mike-ady/Stenokey/Key_Print_Files/FingerWideLeft.stl

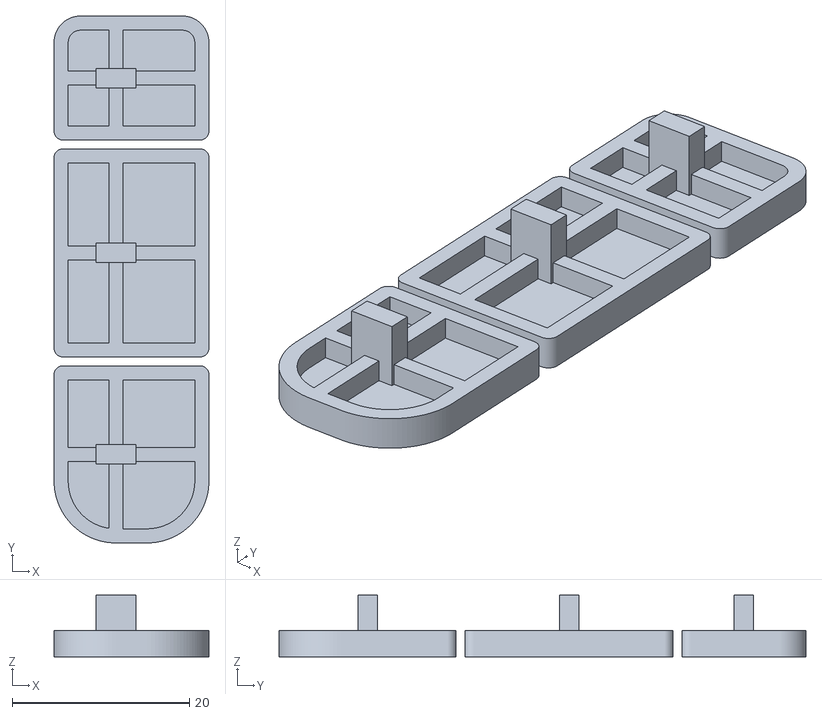
[picture p19: CAD file, 2017-11-08]
Key_Print_Files/FingerWideLeft.stl
17.5 x 59.5 x 7.00
