mike-ady/Stenokey/PCB.stl

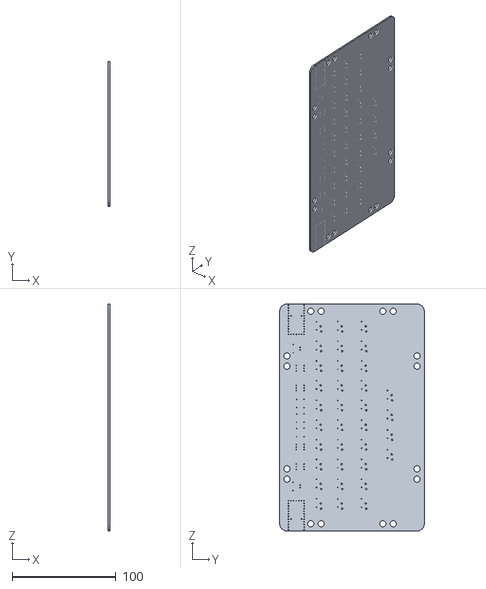
[picture p20: CAD file, 2017-11-08]
PCB.stl
1.60 x 139.5 x 219.0
