mike-ady/Stenokey/Key_Print_Files/KeyUpperWideLeftExtended.stl

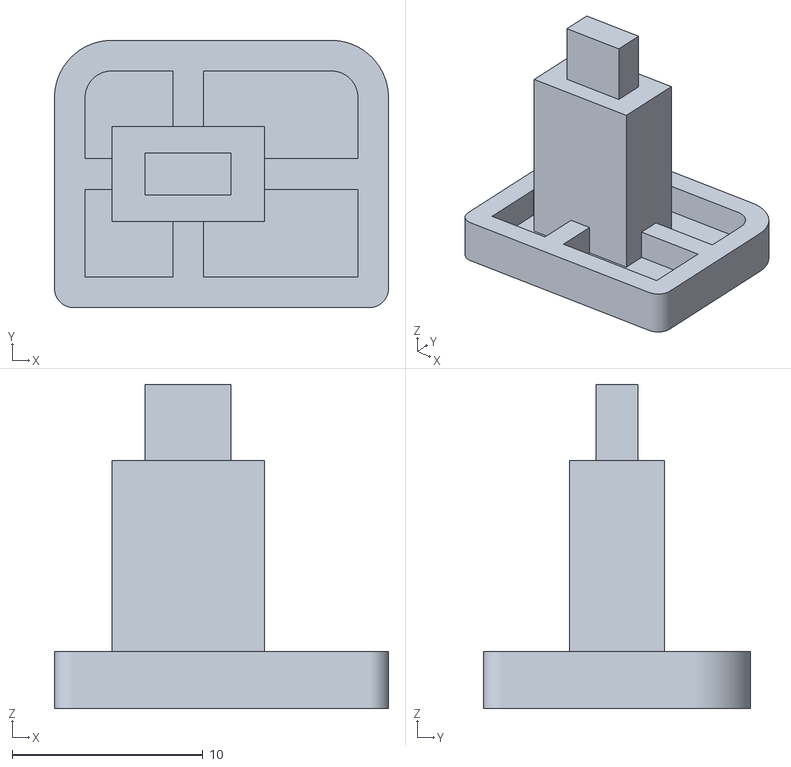
[picture p21: CAD file, 2017-11-08]
Key_Print_Files/KeyUpperWideLeftExtended.stl
17.5 x 14.0 x 17.0
