mike-ady/Stenokey/Key_Print_Files/KeyLowerWideLeftExtended.stl

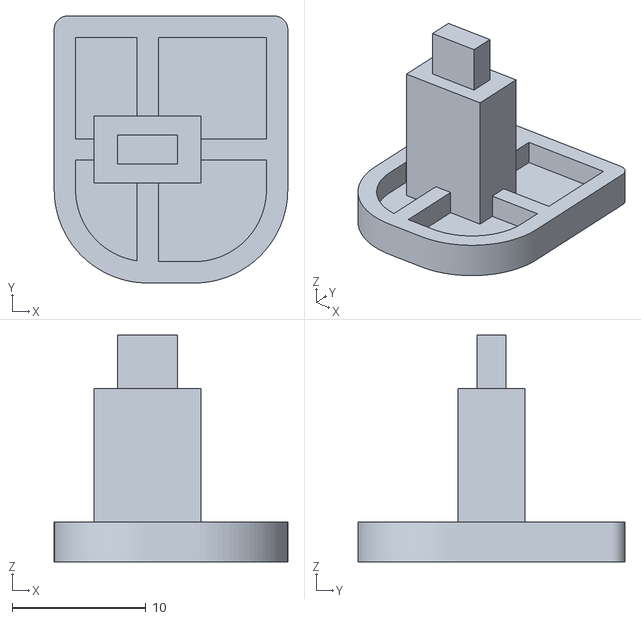
[picture p22: CAD file, 2017-11-08]
Key_Print_Files/KeyLowerWideLeftExtended.stl
17.5 x 20.0 x 17.0
