mike-ady/Stenokey/Key_Print_Files/KeyMiddleWideRightExtended.stl

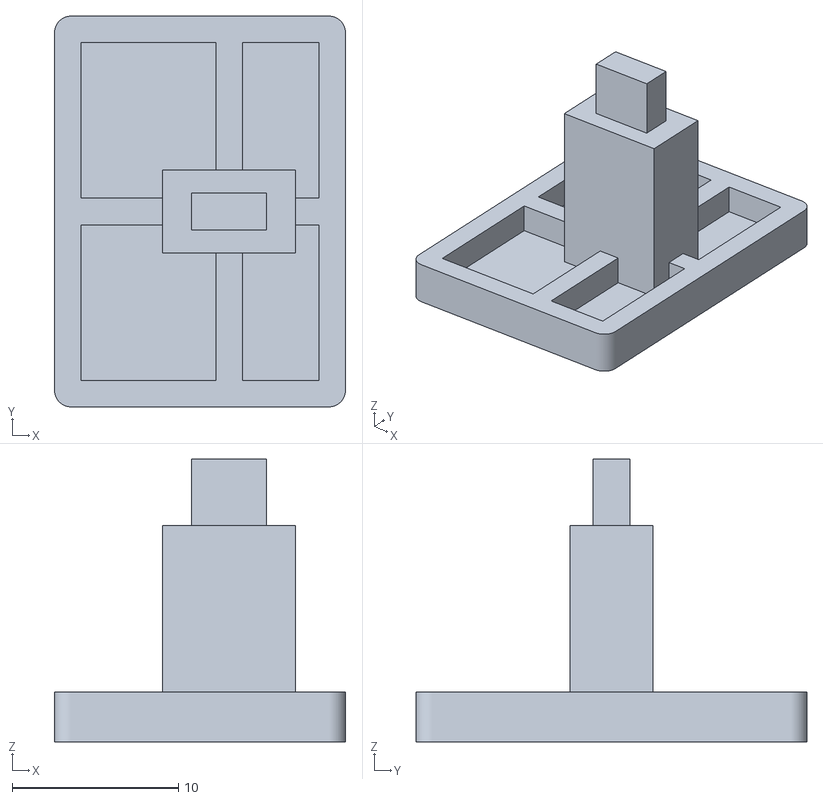
[picture p23: CAD file, 2017-11-08]
Key_Print_Files/KeyMiddleWideRightExtended.stl
17.5 x 23.5 x 17.0
