mike-ady/Stenokey/Key_Print_Files/FingerNarrow.stl

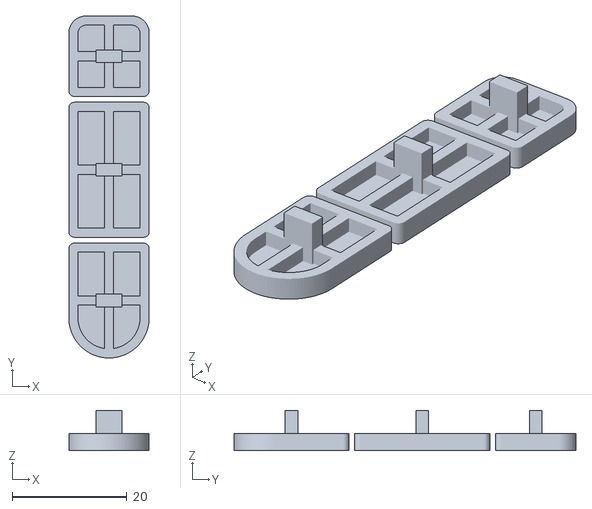
[picture p24: CAD file, 2017-11-08]
Key_Print_Files/FingerNarrow.stl
14.0 x 59.5 x 7.00
