mike-ady/Stenokey/Key_Print_Files/KeyLowerDouble.stl

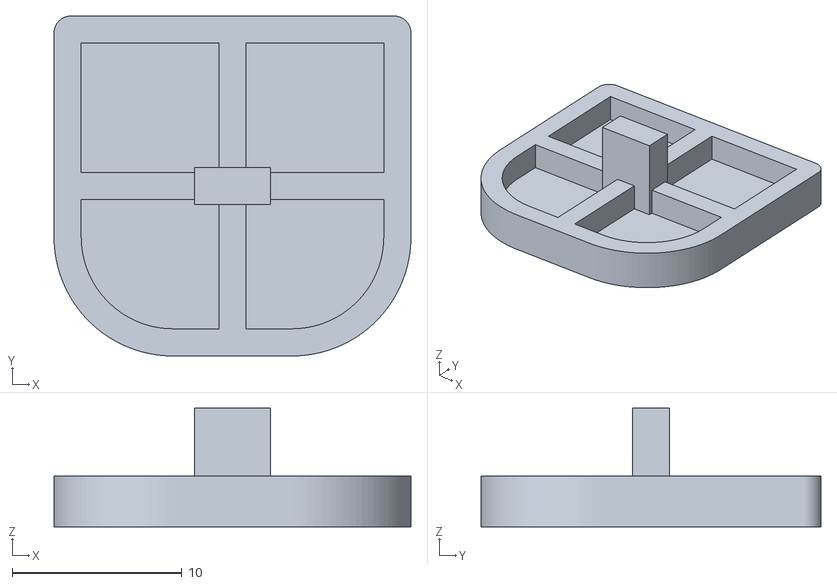
[picture p25: CAD file, 2017-11-08]
Key_Print_Files/KeyLowerDouble.stl
21.0 x 20.0 x 7.00
