mike-ady/Stenokey/Key_Print_Files/FingerDouble.stl

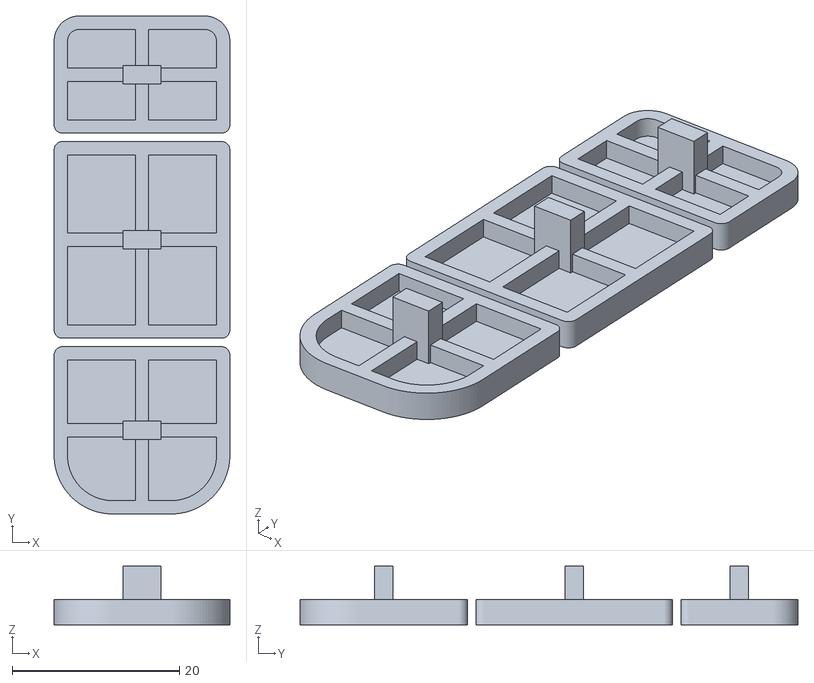
[picture p26: CAD file, 2017-11-08]
Key_Print_Files/FingerDouble.stl
21.0 x 59.5 x 7.00
