mike-ady/Stenokey/Key_Print_Files/KeyUpperNarrowExtended.stl

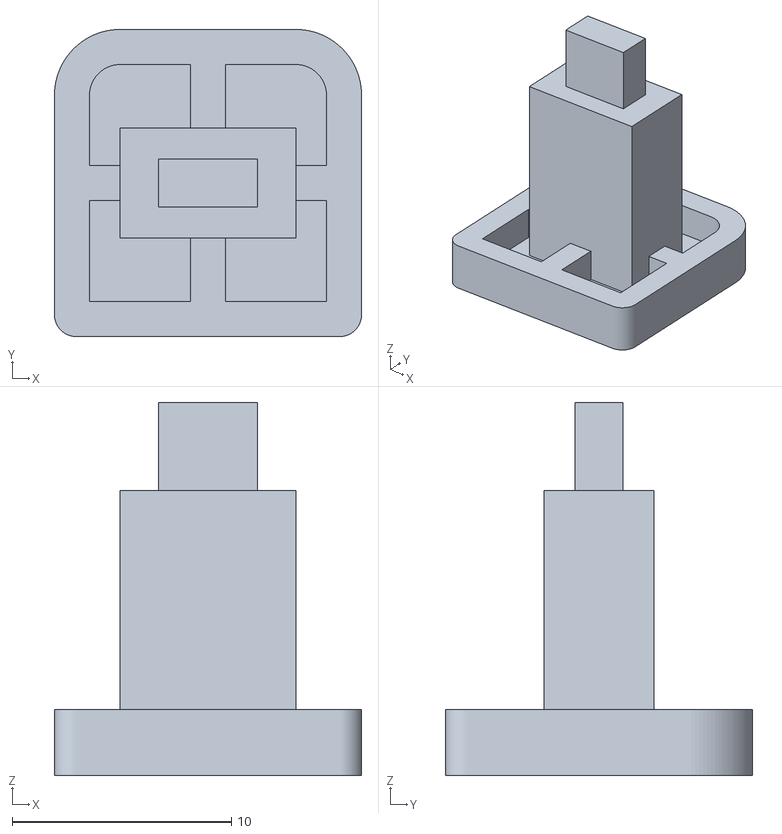
[picture p27: CAD file, 2017-11-08]
Key_Print_Files/KeyUpperNarrowExtended.stl
14.0 x 14.0 x 17.0
