mike-ady/Stenokey/Key_Print_Files/KeyMiddleWideRight.stl

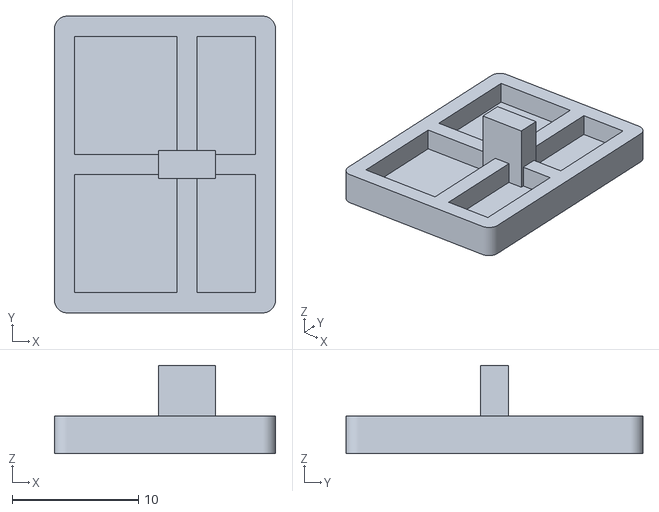
[picture p28: CAD file, 2017-11-08]
Key_Print_Files/KeyMiddleWideRight.stl
17.5 x 23.5 x 7.00
