mike-ady/Stenokey/Key_Print_Files/KeyUpperDouble.stl

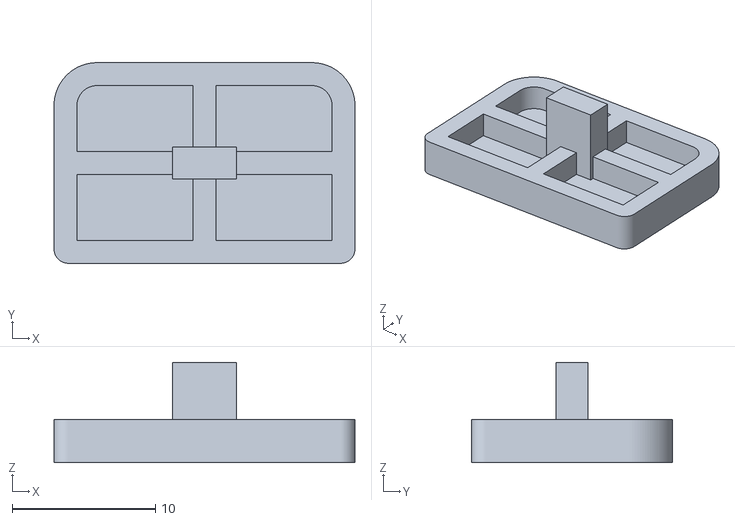
[picture p29: CAD file, 2017-11-08]
Key_Print_Files/KeyUpperDouble.stl
21.0 x 14.0 x 7.00
