mike-ady/Stenokey/Key_Print_Files/FingerNarrowExtended.stl

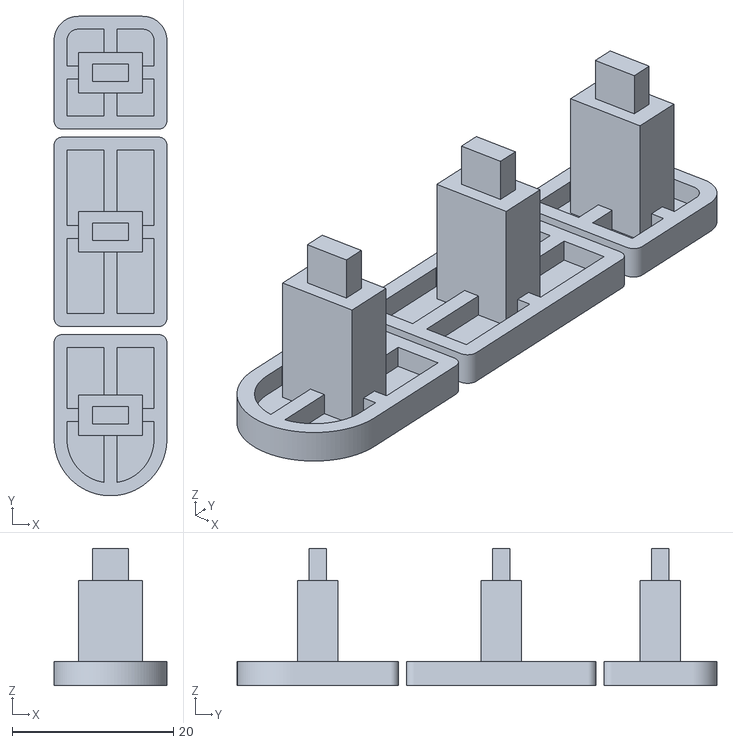
[picture p30: CAD file, 2017-11-08]
Key_Print_Files/FingerNarrowExtended.stl
14.0 x 59.5 x 17.0
