mike-ady/Stenokey/Key_Print_Files/KeyLowerNarrow.stl

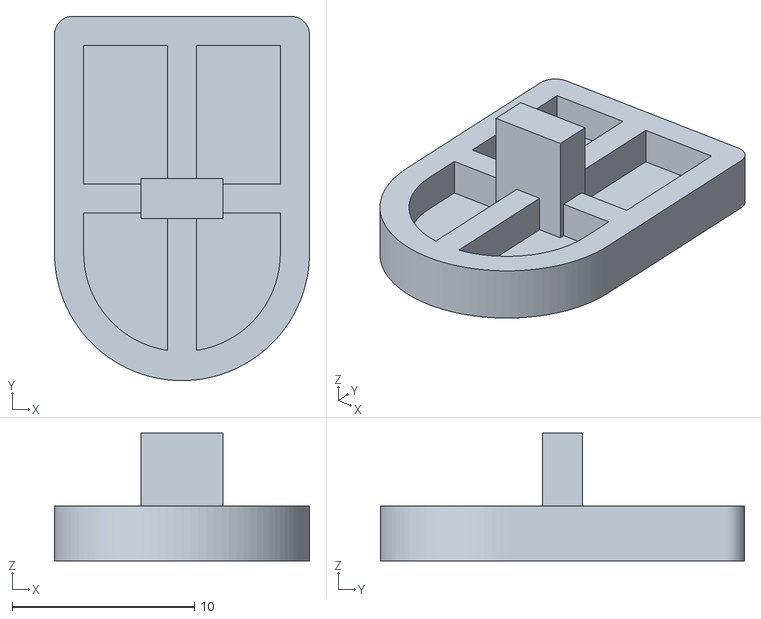
[picture p31: CAD file, 2017-11-08]
Key_Print_Files/KeyLowerNarrow.stl
14.0 x 20.0 x 7.00
