mike-ady/Stenokey/Key_Print_Files/KeyLowerWideLeft.stl

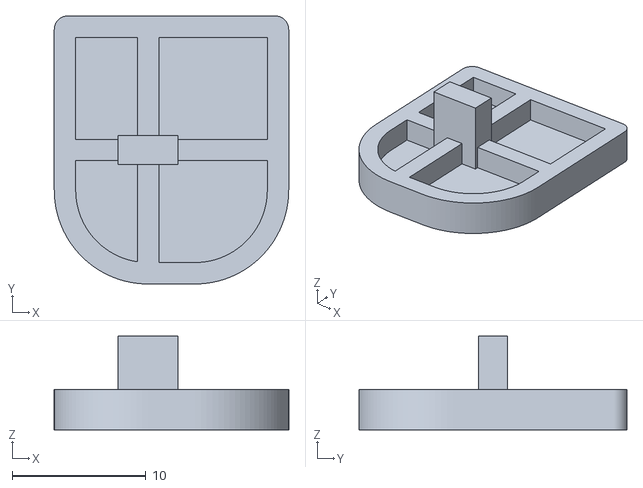
[picture p32: CAD file, 2017-11-08]
Key_Print_Files/KeyLowerWideLeft.stl
17.5 x 20.0 x 7.00
