mike-ady/Stenokey/Key_Print_Files/KeyLowerDoubleExtended.stl

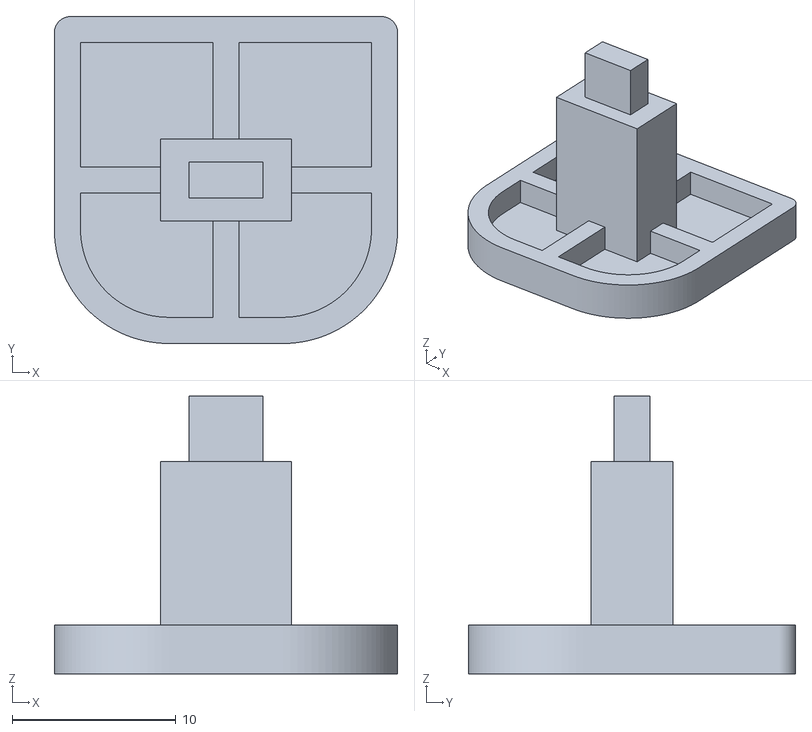
[picture p33: CAD file, 2017-11-08]
Key_Print_Files/KeyLowerDoubleExtended.stl
21.0 x 20.0 x 17.0
