mike-ady/Stenokey/Key_Print_Files/KeyUpperDoubleExtended.stl

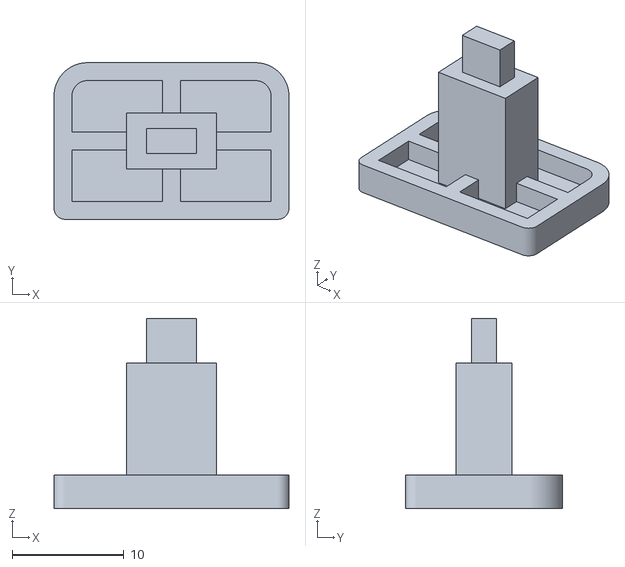
[picture p34: CAD file, 2017-11-08]
Key_Print_Files/KeyUpperDoubleExtended.stl
21.0 x 14.0 x 17.0
