mike-ady/Stenokey/Key_Print_Files/KeyUpperNarrow.stl

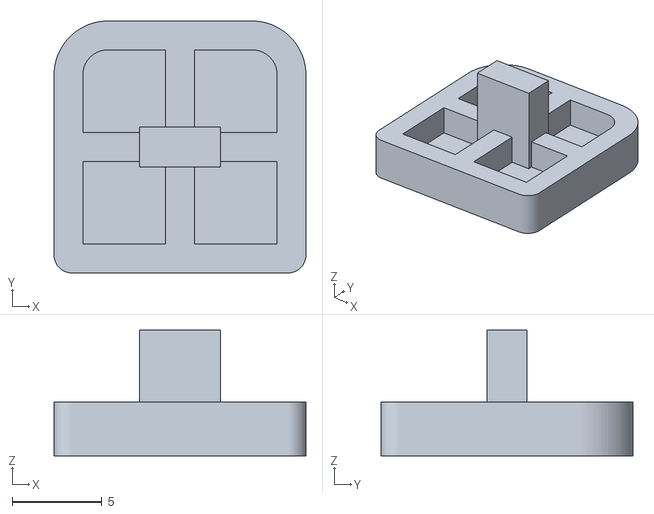
[picture p35: CAD file, 2017-11-08]
Key_Print_Files/KeyUpperNarrow.stl
14.0 x 14.0 x 7.00
