mike-ady/Stenokey/Key_Print_Files/Test Stand.stl

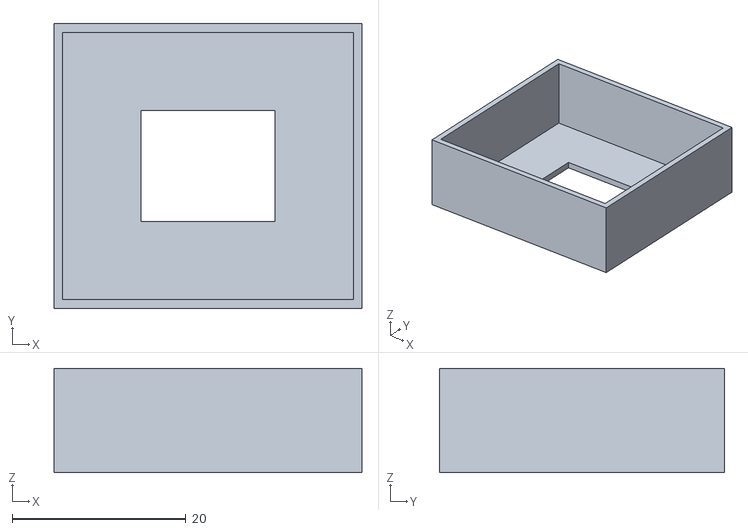
[picture p36: CAD file, 2017-11-08]
Key_Print_Files/Test Stand.stl
35.5 x 32.8 x 12.0
