mike-ady/Stenokey/Key_Print_Files/KeyMiddleNarrow.stl

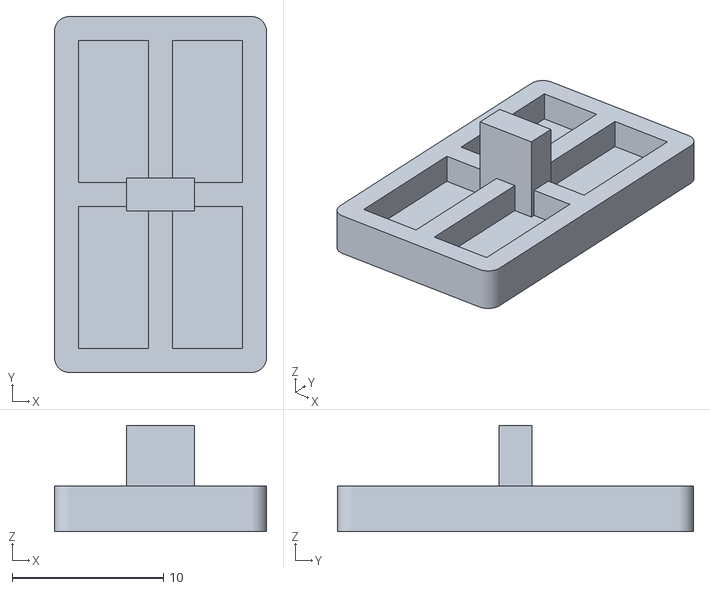
[picture p37: CAD file, 2017-11-08]
Key_Print_Files/KeyMiddleNarrow.stl
14.0 x 23.5 x 7.00
