mike-ady/Stenokey/Key_Print_Files/KeyMiddleDouble.stl

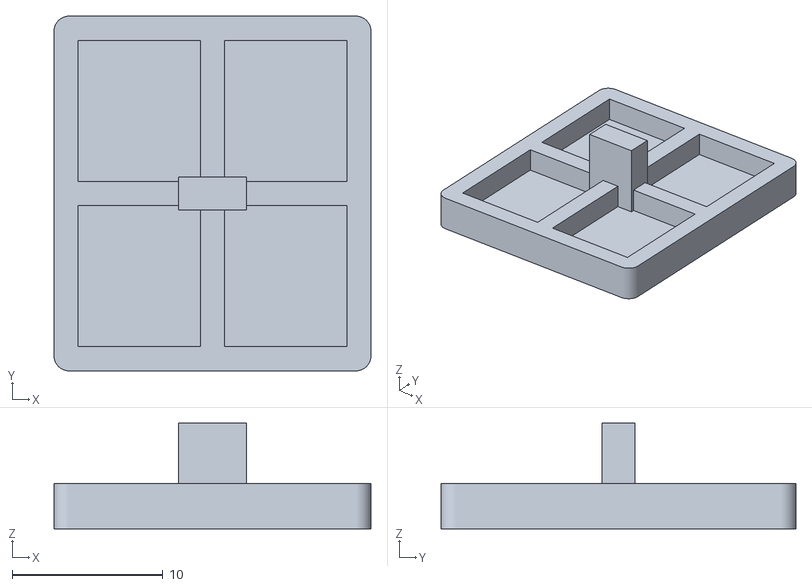
[picture p38: CAD file, 2017-11-08]
Key_Print_Files/KeyMiddleDouble.stl
21.0 x 23.5 x 7.00
